HowardsPlayPen/Project5-ESP32-WROOM-PZEM/Software/ESP32-WROOM-Waveshare-2.9-epaper-test/src/epdif.cpp

/**
 *  @filename   :   epdif.cpp
 *  @brief      :   Implements EPD interface functions
 *                  Users have to implement all the functions in epdif.cpp
 *  @author     :   Yehui from Waveshare
 *
 *  Copyright (C) Waveshare     August 10 2017
 *
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
 * THE SOFTWARE IS PROVIDED "AS IS", WITHOUT WARRANTY OF ANY KIND, EXPRESS OR
 * IMPLIED, INCLUDING BUT NOT LIMITED TO THE WARRANTIES OF MERCHANTABILITY,
 * FITNESS OR A PARTICULAR PURPOSE AND NONINFRINGEMENT. IN NO EVENT SHALL THE
 * AUTHORS OR COPYRIGHT HOLDERS BE LIABLE FOR ANY CLAIM, DAMAGES OR OTHER
 * LIABILITY WHETHER IN AN ACTION OF CONTRACT, TORT OR OTHERWISE, ARISING FROM,
 * OUT OF OR IN CONNECTION WITH THE SOFTWARE OR THE USE OR OTHER DEALINGS IN
 * THE SOFTWARE.
 */

#include "epdif.h"
#include <SPI.h>

EpdIf::EpdIf() {};

SPIClass * EpdIf::mySpi;

EpdIf::~EpdIf() {
};

void EpdIf::DigitalWrite(int pin, int value) {
    digitalWrite(pin, value);
}

int EpdIf::DigitalRead(int pin) {
    return digitalRead(pin);
}

void EpdIf::DelayMs(unsigned int delaytime) {
    delay(delaytime);
}

void EpdIf::SpiTransfer(unsigned char data) {
    digitalWrite(CS_PIN, LOW);
    mySpi->transfer(data);
    digitalWrite(CS_PIN, HIGH);
}

int EpdIf::IfInit(void) {
    pinMode(CS_PIN, OUTPUT);
    pinMode(RST_PIN, OUTPUT);
    pinMode(DC_PIN, OUTPUT);
    pinMode(BUSY_PIN, INPUT); 
    mySpi->begin();
    mySpi->beginTransaction(SPISettings(2000000, MSBFIRST, SPI_MODE0));
    return 0;
}
